russells/hc2/hc.c

#include "qpn_port.h"
#include "hc.h"
#include "buttons.h"
#include "bsp.h"
#include "lcd.h"
#include "recorder.h"
#include "rtc.h"
#include "ui.h"
#include "serial.h"


Q_DEFINE_THIS_FILE;


static QEvent rtcQueue[4];
static QEvent recorderQueue[4];
/** The size of buttonsQueue[] is embarrassing, and reveals a flaw in the
    current code.  It will go away completely in a later iteration. */
static QEvent buttonsQueue[18];
static QEvent uiQueue[8];

QActiveCB const Q_ROM Q_ROM_VAR QF_active[] = {
	{ (QActive*)0            , (QEvent*)0   , 0                   },
	{ (QActive *) (&recorder), recorderQueue, Q_DIM(recorderQueue)},
	{ (QActive *) (&buttons) , buttonsQueue , Q_DIM(buttonsQueue) },
	{ (QActive *) (&ui)      , uiQueue      , Q_DIM(uiQueue)      },
	{ (QActive *) (&rtc)     , rtcQueue     , Q_DIM(rtcQueue)     },
};
Q_ASSERT_COMPILE( QF_MAX_ACTIVE == Q_DIM(QF_active) - 1 );


int main(void)
{
	/**
	 * Reserve this space for recording assertions.  We don't touch this
	 * memory here, and assume that it will be in the same place on every
	 * run, and that it isn't cleared by hardware or by startup code.  If
	 * those are true, then after a reset caused by an assertion, it will
	 * contain the values as filled in by QF_onAssert() at the end of the
	 * previous run (before the reset).
	 *
	 * FIXME: test the assumptions.  Also test hardware reset.
	 */
	struct AssertionBuffer assertion_buffer;
	BSP_set_assertion_buffer(&assertion_buffer);

 startmain:
	BSP_init();
	serial_init();
	SERIALSTR("\r\n\r\n*** Hots and Colds ***\r\n");
	buttons_ctor();
	rtc_ctor();
	lcd_init();
	recorder_ctor();
	ui_ctor();
	SERIALSTR("Let's go...\r\n");
	QF_run();
	goto startmain;

	return 0;
}
