russells/hc2/buttons.h

#ifndef buttons_h_INCLUDED
#define buttons_h_INCLUDED

#include "qpn_port.h"
#include "hc.h"


struct Button {
	QHsm super;
	QSignal press_signal;
	QSignal long_press_signal;
	QSignal repeat_signal;
	QSignal release_signal;
	uint8_t counter;
};


struct Buttons {
	QActive super;
	struct Button button1;
	struct Button button2;
	struct Button button3;
	struct Button button4;
	uint8_t up_counter;
};


extern struct Buttons buttons;

void buttons_ctor(void);

#endif
